probe-rs/rusty-probe/math/pwm_dac.asc

C1: cap; 100n
C2: cap; 100n
C3: cap; 2.2µ
C4: cap; 10p
R1: res; 17.4k
R2: res; 5.1k
R3: res; 47k
R4: res; 33k
R5: res; 47k
R6: res; 500
U1: ADM7170
V1: voltage; PULSE(0 3.3 20m 100n 100n 40u 50u)
V2: voltage; 5V
Named nets: 0, Vset
.tran 100m startup
